jacky4566/Veridian-Heliograph/Firmware/STM32IDE/Heliograph_L432/Core/Inc/myApp.h

/*
 * myApp.h
 *
 *  Created on: May 29, 2022
 *      Author: jacks
 */

#ifndef INC_MYAPP_H_
#define INC_MYAPP_H_

#include <stdbool.h>
#include <stdlib.h>
#include <time.h>
#include <math.h>

//External Variables
extern volatile uint32_t superCapmV;
extern volatile int tempC;
extern volatile uint32_t guiTimer;

#define LCD_RATE_SLOW  (15)
#define mV_OV		   ((uint16_t) 4100 )
#define mV_GNSS_FAST   ((uint16_t) 3600 )
#define mV_GNSS_SLOW   ((uint16_t) 3000 )
#define mV_GNSS_OFF    ((uint16_t) 2900 )
#define mV_LCD_ON      ((uint16_t) 2800 )
#define mV_LCD_OFF     ((uint16_t) 2600 )

typedef enum {
	WKUP_CLEAR, WKUP_LPUART, WKUP_RTC, WKUP_EXTIO, WKUP_ADC
} wakeUpSource;

extern wakeUpSource lastWakeUpSource;

//functions
void myApp_init();
void myApp_loop();
struct tm getTime();
void setTimeGNSS();

enum ADC_State_enum getADCState();
bool vBATOK();

#endif /* INC_MYAPP_H_ */
