jacky4566/Veridian-Heliograph/Firmware/STM32IDE/Heliograph_LCD_Dev/Core/Inc/myApp.h

/*
 * myApp.h
 *
 *  Created on: May 29, 2022
 *      Author: jacks
 */

#ifndef INC_MYAPP_H_
#define INC_MYAPP_H_

#include <stdbool.h>

//External Variables
extern volatile int16_t superCapmV;
extern volatile int32_t tempC;
extern volatile uint32_t guiTimer;

#define LCD_RATE_FAST  (1)
#define LCD_RATE_SLOW  (15)
#define mV_OV		   ((int16_t) 3500 )
#define mV_GNSS_ON     ((int16_t) 3400 )
#define mV_GNSS_OFF    ((int16_t) 3000 )
#define mV_LCD_OFF     ((int16_t) 2500 )
#define mV_LCD_SLOW    ((int16_t) 2750 )
#define mV_LCD_FAST    ((int16_t) 3000 )

typedef enum {
	WKUP_CLEAR, WKUP_LPUART, WKUP_RTC, WKUP_EXTIO, WKUP_ADC
} wakeUpSource;

extern wakeUpSource lastWakeUpSource;

//functions
void myApp_init();
void myApp_loop();
struct tm getTime();
void setTimeGNSS();

enum ADC_State_enum getADCState();
bool vBATOK();

#endif /* INC_MYAPP_H_ */
